mark-belbin/e-sup/mechanical/battery/HOLDER, PCBA, ASM.SLDASM

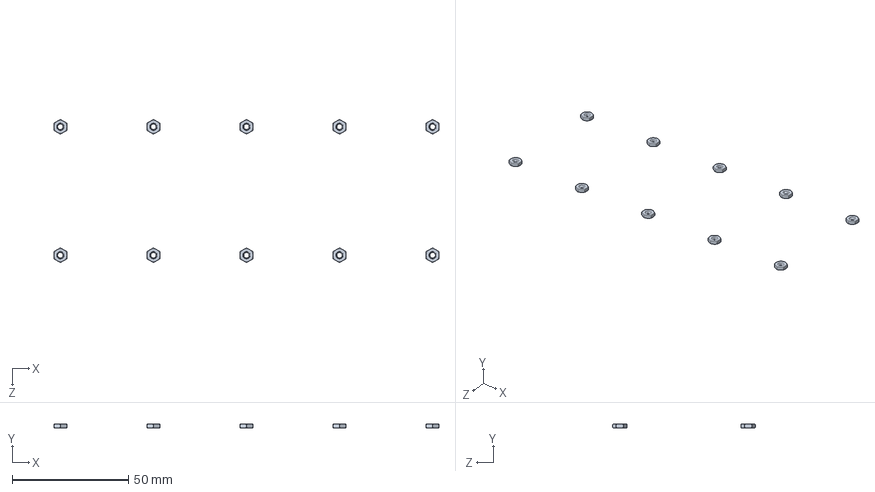
[picture p3: CAD file, 2023-11-13]
mechanical/battery/HOLDER, PCBA, ASM.SLDASM
165.5 x 1.80 x 61.6 mm
NUT, M3, THIN, 90370A203 x 10
