mark-belbin/e-sup/mechanical/battery/HOLDER, DUAL, ASM.SLDASM

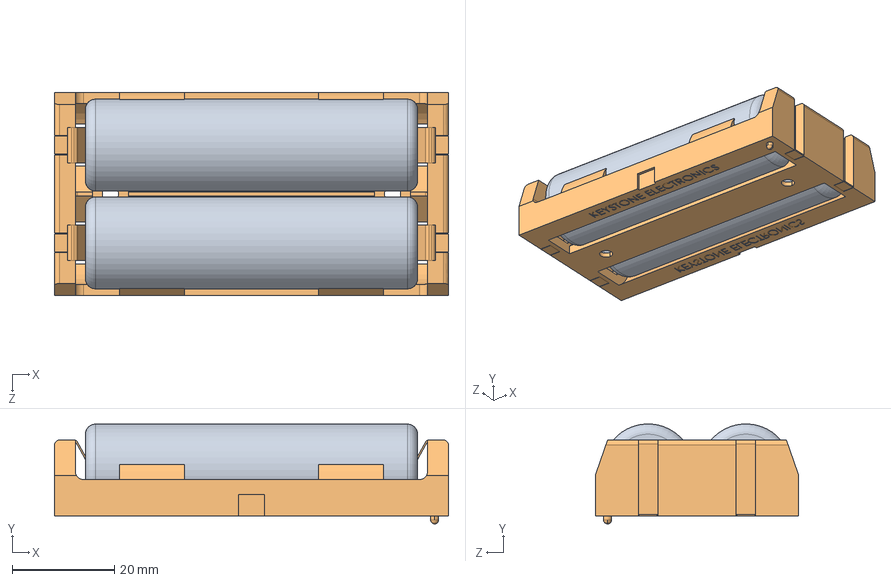
[picture p4: CAD file, 2023-11-13]
mechanical/battery/HOLDER, DUAL, ASM.SLDASM
77.1 x 19.5 x 39.8 mm
HOLDER, DUAL, KEYSTONE
BATTERY, 18650 x 2
