mark-belbin/e-sup/mechanical/battery/HOLDER, SINGLE, ASM.SLDASM

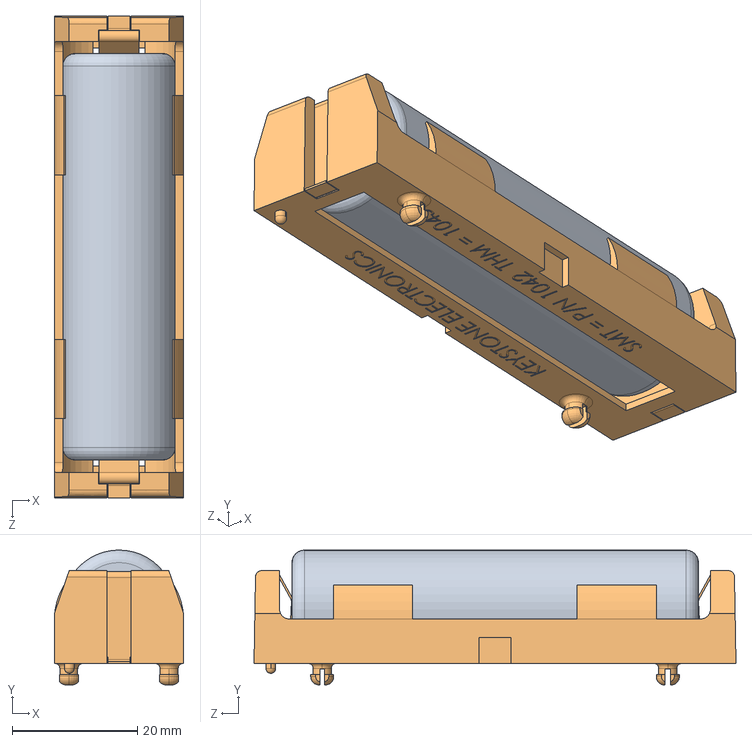
[picture p6: CAD file, 2023-10-09]
mechanical/battery/HOLDER, SINGLE, ASM.SLDASM
20.7 x 21.6 x 77.1 mm
HOLDER, SINGLE, KEYSTONE
BATTERY, 18650
