mark-belbin/e-sup/mechanical/ots_hardware/NUT, M3, THIN, 90370A203.SLDPRT

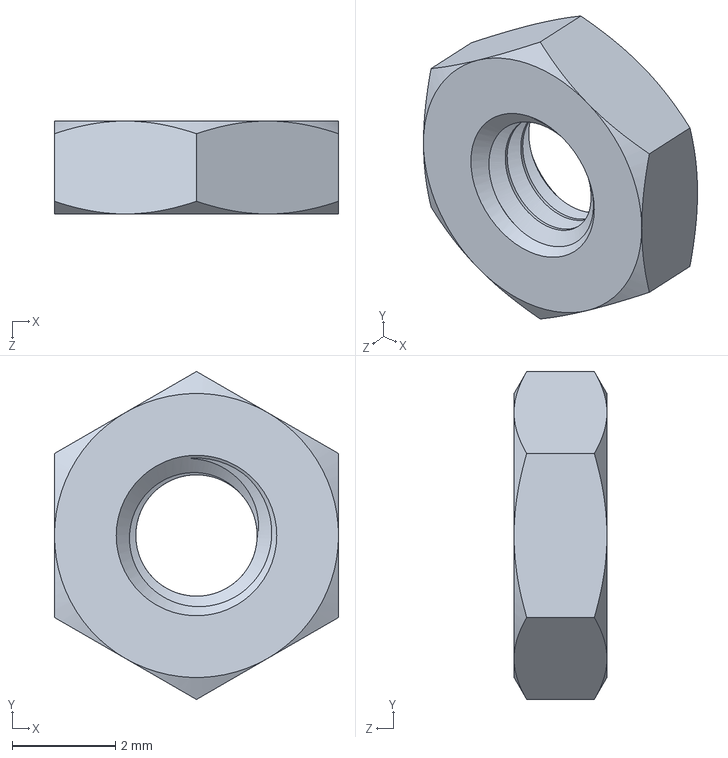
[picture p18: CAD file, 2023-10-09]
mechanical/ots_hardware/NUT, M3, THIN, 90370A203.SLDPRT
5.50 x 6.35 x 1.80 mm
