mark-belbin/e-sup/hardware/bms/3d_models/CUI_DEVICES_DS04-254-2-01BK-SMT-TR.step

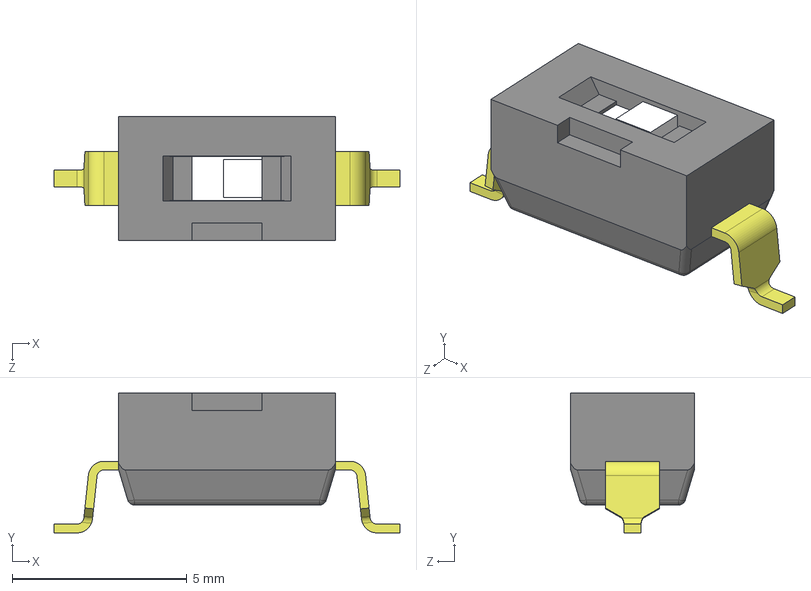
[picture p19: CAD file, 2024-04-14]
hardware/bms/3d_models/CUI_DEVICES_DS04-254-2-01BK-SMT-TR.step
9.90 x 4.00 x 3.54 mm
