mark-belbin/e-sup/mechanical/blue_robotics/WLP-M14-9.5MM-PUBLIC.SLDPRT

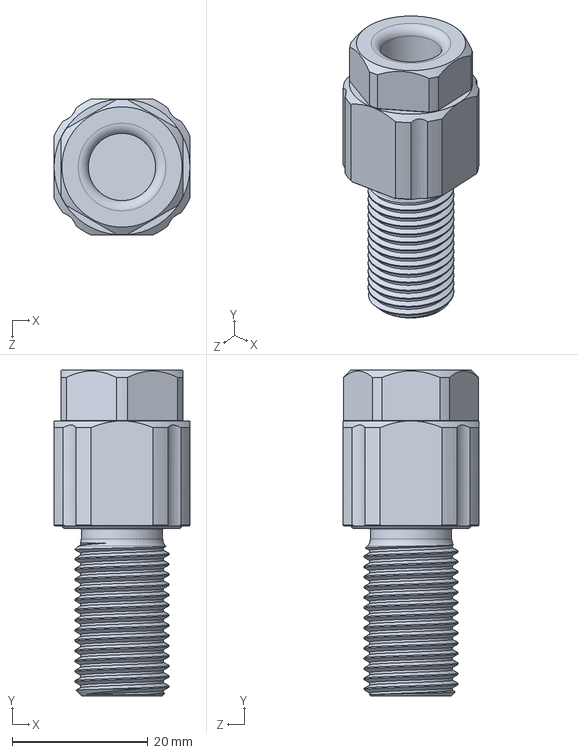
[picture p20: CAD file, 2023-10-09]
mechanical/blue_robotics/WLP-M14-9.5MM-PUBLIC.SLDPRT
20.0 x 48.0 x 20.0 mm
