mark-belbin/e-sup/mechanical/enclosure/ENCLOSURE, BODY.SLDPRT

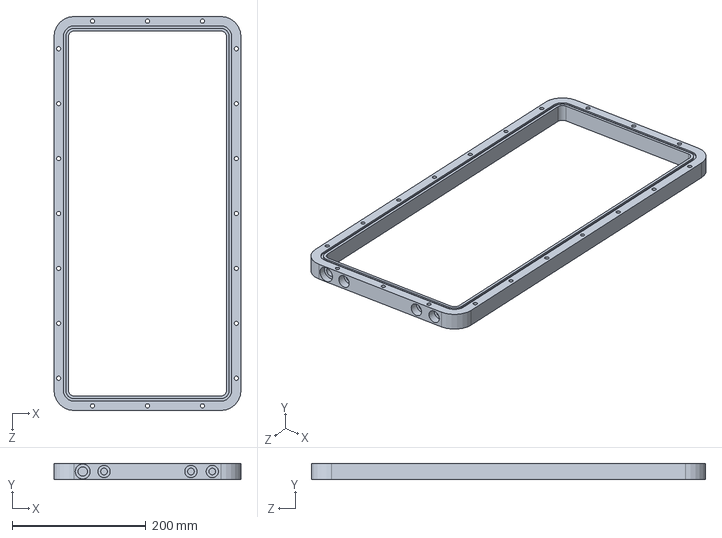
[picture p21: CAD file, 2023-10-09]
mechanical/enclosure/ENCLOSURE, BODY.SLDPRT
280.0 x 24.1 x 590.0 mm
