mark-belbin/e-sup/mechanical/battery/PCB, 11X BATTERY HOLDER.SLDPRT

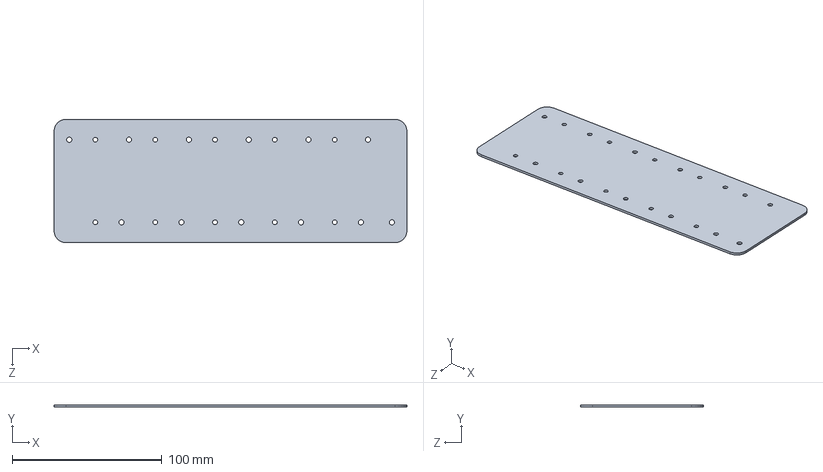
[picture p22: CAD file, 2023-10-31]
mechanical/battery/PCB, 11X BATTERY HOLDER.SLDPRT
236.0 x 1.60 x 82.5 mm
