mark-belbin/e-sup/mechanical/enclosure/ENCLOSURE, BASE.SLDPRT

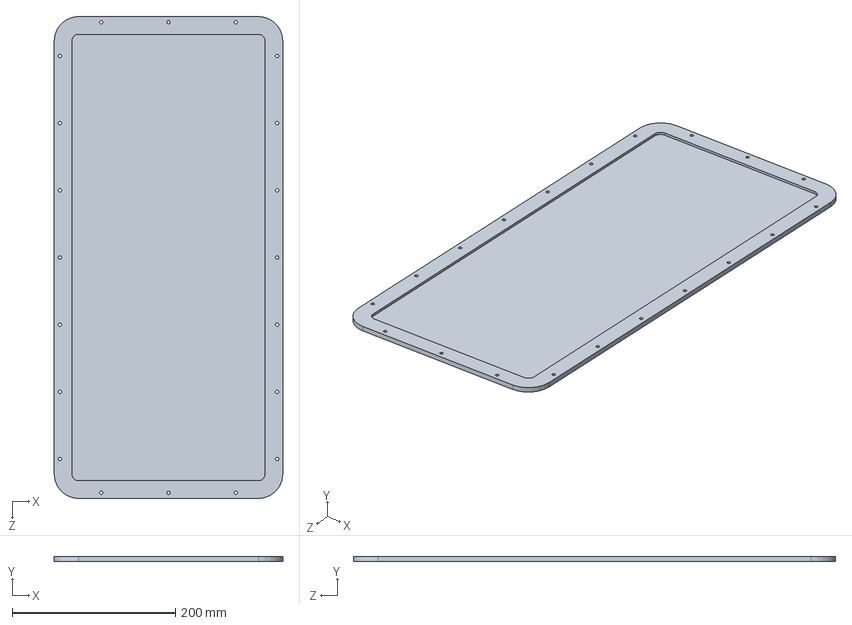
[picture p23: CAD file, 2023-10-09]
mechanical/enclosure/ENCLOSURE, BASE.SLDPRT
280.0 x 6.00 x 590.0 mm
