mark-belbin/e-sup/mechanical/battery/PCB, BMS.SLDPRT

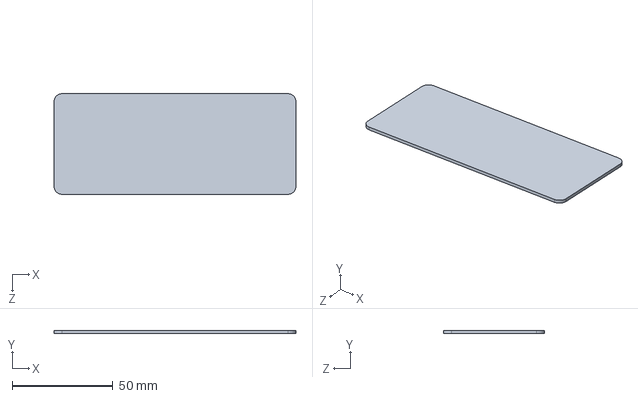
[picture p24: CAD file, 2023-10-31]
mechanical/battery/PCB, BMS.SLDPRT
120.0 x 1.60 x 50.0 mm
