mark-belbin/e-sup/mechanical/blue_robotics/SWITCH-M10-5A-R1-RP.SLDPRT

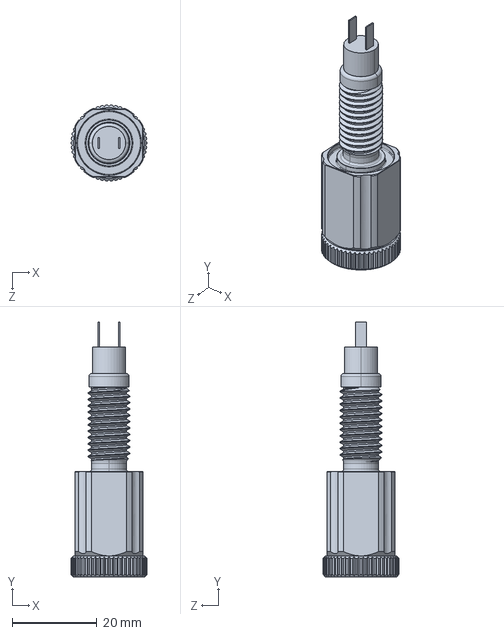
[picture p25: CAD file, 2023-10-09]
mechanical/blue_robotics/SWITCH-M10-5A-R1-RP.SLDPRT
18.0 x 60.3 x 18.0 mm
