mark-belbin/e-sup/mechanical/enclosure/ENCLOSURE, LID.SLDPRT

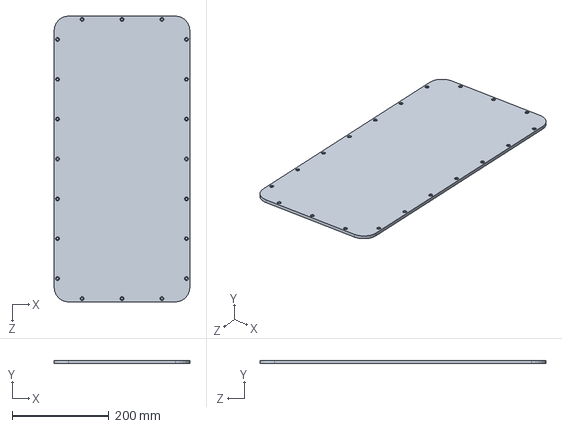
[picture p26: CAD file, 2023-10-09]
mechanical/enclosure/ENCLOSURE, LID.SLDPRT
280.0 x 6.35 x 590.0 mm
