mark-belbin/e-sup/mechanical/ots_hardware/INSERT, M4, 92398A123.SLDPRT

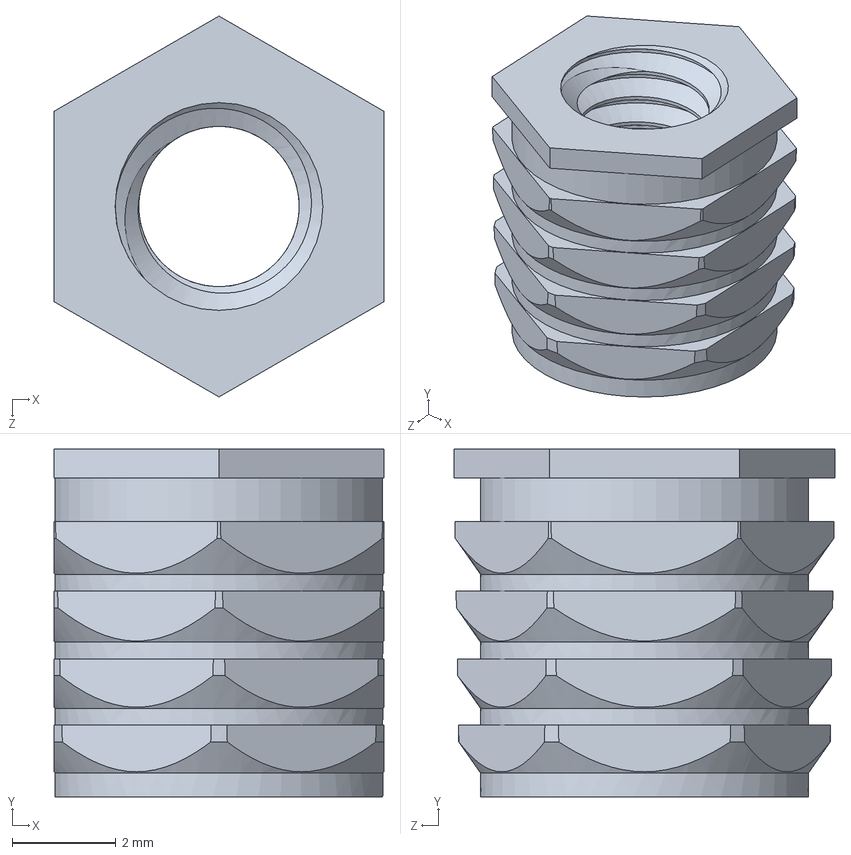
[picture p27: CAD file, 2023-10-09]
mechanical/ots_hardware/INSERT, M4, 92398A123.SLDPRT
6.35 x 6.70 x 7.33 mm
