mark-belbin/e-sup/hardware/bms/3d_models/SF-3812F-T.stp

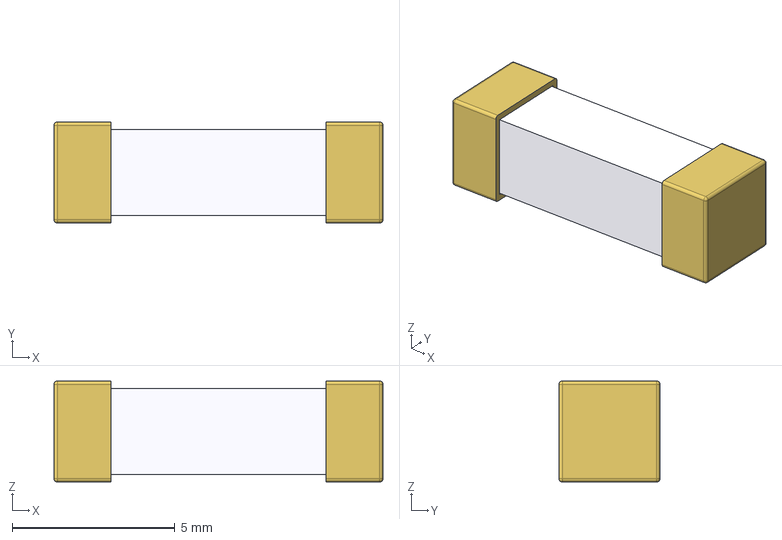
[picture p28: CAD file, 2024-04-14]
hardware/bms/3d_models/SF-3812F-T.stp
10.1 x 3.10 x 3.10 mm
