mark-belbin/e-sup/mechanical/battery/BATTERY, 18650.SLDPRT

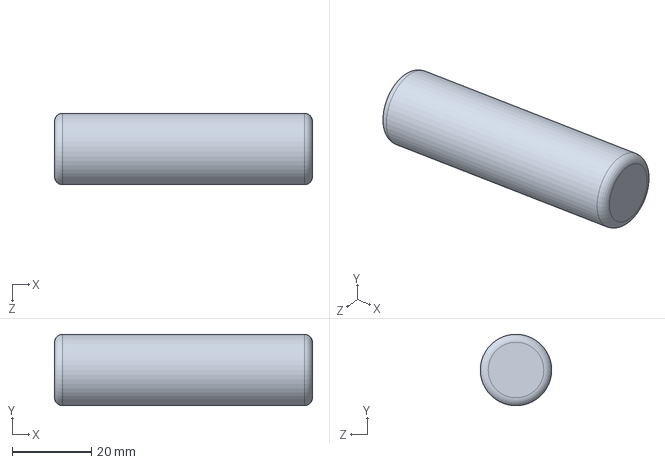
[picture p29: CAD file, 2023-10-09]
mechanical/battery/BATTERY, 18650.SLDPRT
65.0 x 18.0 x 18.0 mm
