mark-belbin/e-sup/mechanical/blue_robotics/WLP-M10-7.5MM-PUBLIC.SLDPRT

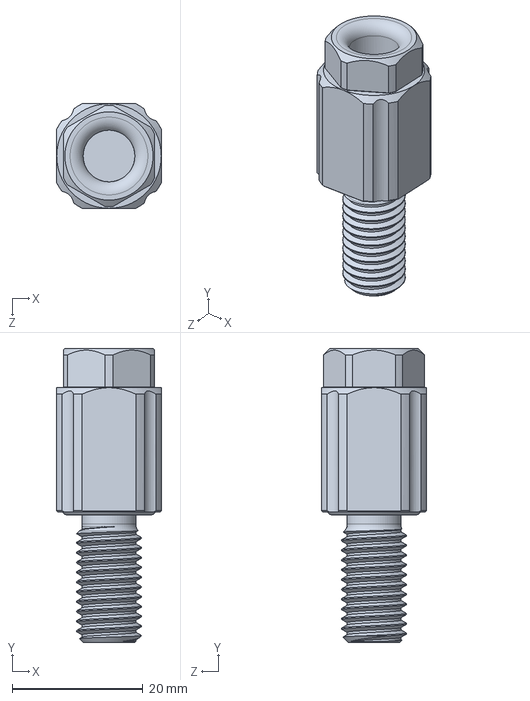
[picture p30: CAD file, 2023-10-09]
mechanical/blue_robotics/WLP-M10-7.5MM-PUBLIC.SLDPRT
16.0 x 45.0 x 16.0 mm
