mark-belbin/e-sup/hardware/bms/3d_models/IND_1050P-WE-PD_WRE.step

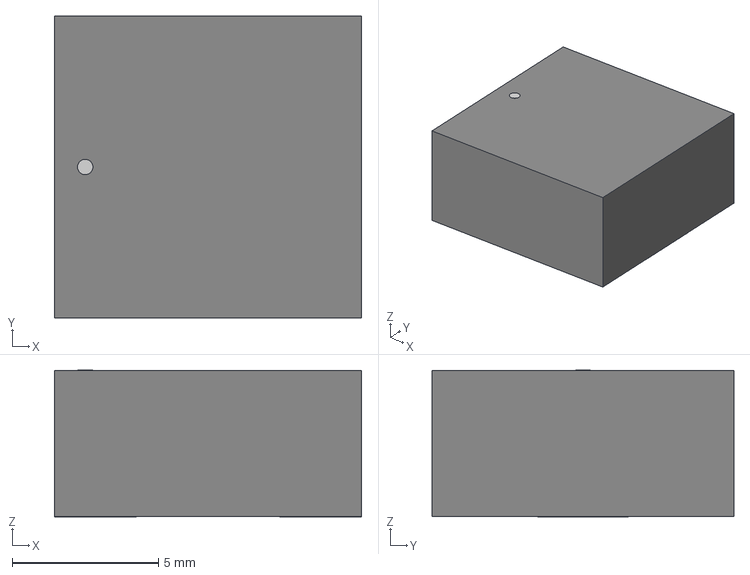
[picture p31: CAD file, 2024-04-14]
hardware/bms/3d_models/IND_1050P-WE-PD_WRE.step
10.5 x 10.3 x 5.01 mm
