mark-belbin/e-sup/mechanical/battery/HOLDER, SINGLE, KEYSTONE.SLDPRT

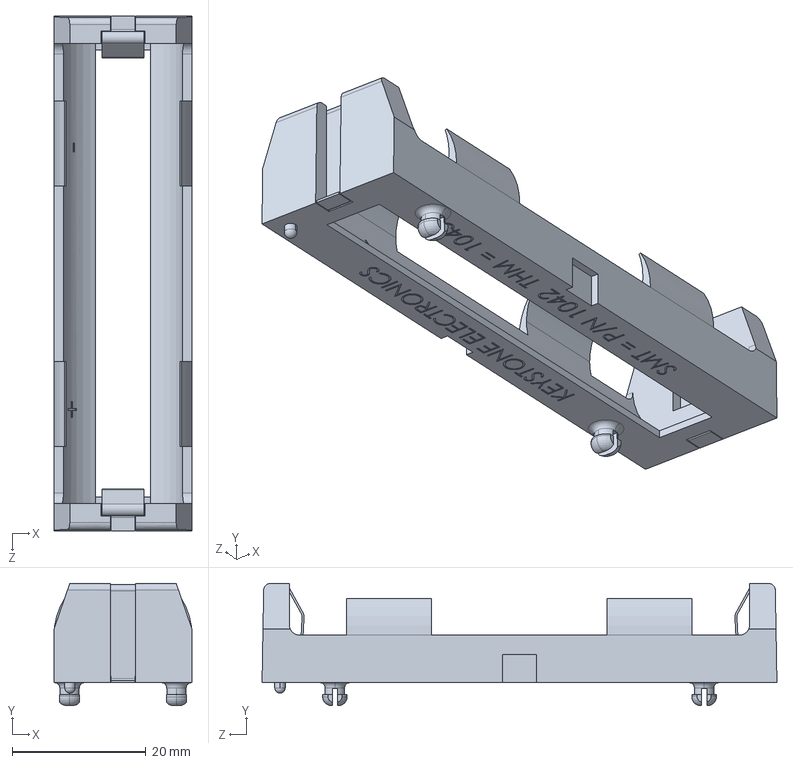
[picture p32: CAD file, 2023-10-09]
mechanical/battery/HOLDER, SINGLE, KEYSTONE.SLDPRT
20.7 x 18.3 x 77.1 mm
