mark-belbin/e-sup/mechanical/blue_robotics/VENT-M10-R1-RP.SLDPRT

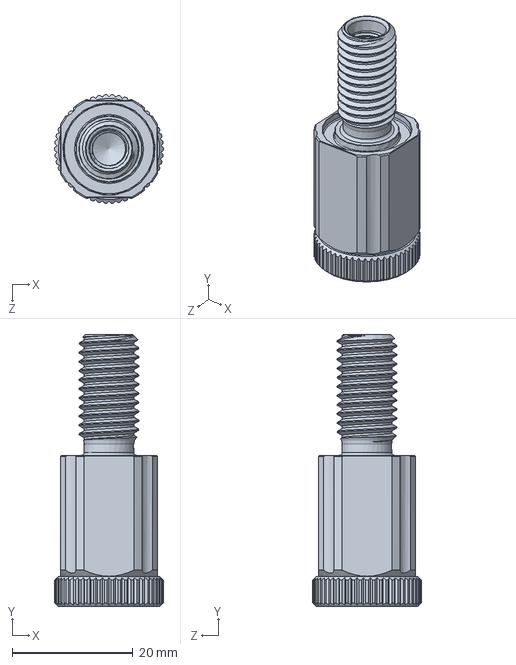
[picture p33: CAD file, 2023-10-09]
mechanical/blue_robotics/VENT-M10-R1-RP.SLDPRT
18.0 x 45.0 x 18.0 mm
