mark-belbin/e-sup/hardware/bms/3d_models/ETQP5M3R3YFK.step

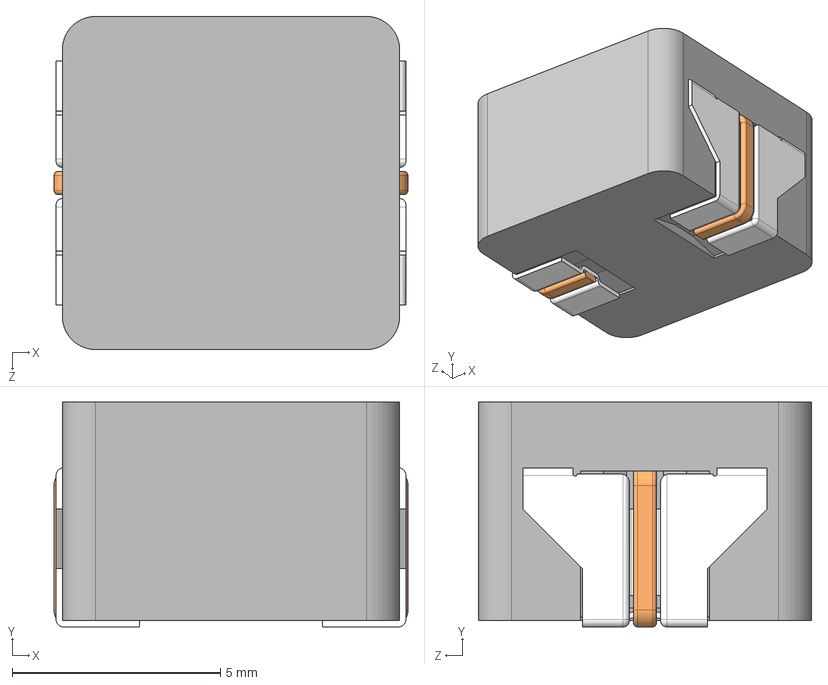
[picture p34: CAD file, 2024-04-14]
hardware/bms/3d_models/ETQP5M3R3YFK.step
8.50 x 5.40 x 8.00 mm
