mark-belbin/e-sup/hardware/bms/3d_models/5019.step

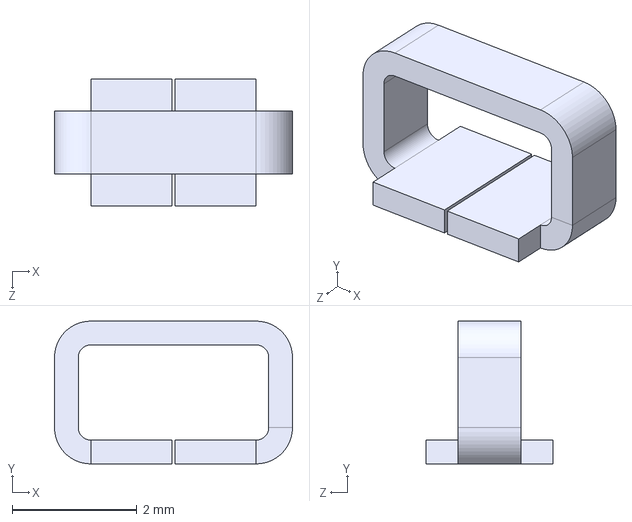
[picture p35: CAD file, 2024-04-14]
hardware/bms/3d_models/5019.step
3.81 x 2.29 x 2.03 mm
