mark-belbin/e-sup/hardware/bms/3d_models/usb4110-gf-a.stp

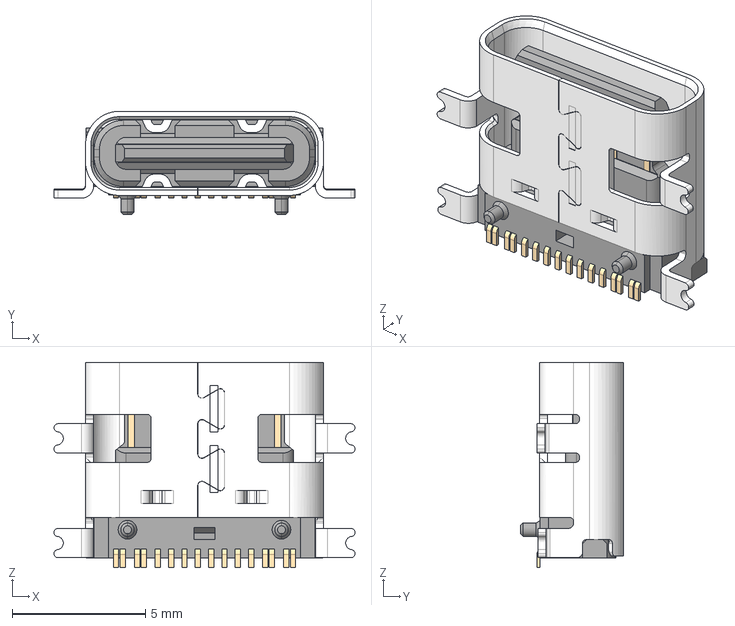
[picture p36: CAD file, 2024-04-14]
hardware/bms/3d_models/usb4110-gf-a.stp
11.3 x 3.89 x 7.70 mm
