mark-belbin/e-sup/hardware/bms/3d_models/B3U-1000P.step

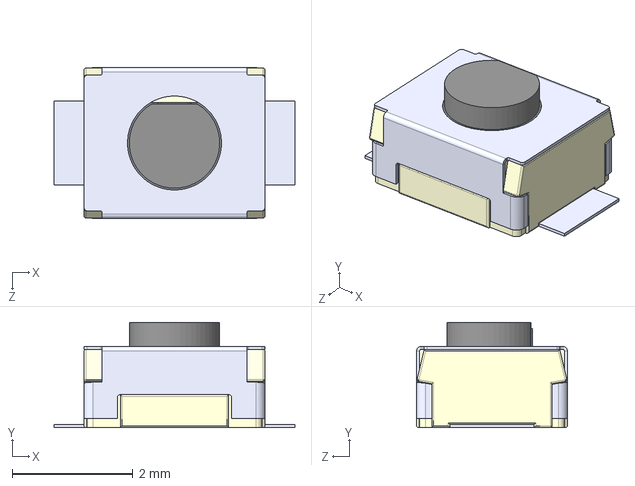
[picture p37: CAD file, 2024-04-14]
hardware/bms/3d_models/B3U-1000P.step
4.00 x 1.75 x 2.50 mm
