mark-belbin/e-sup/hardware/bms/3d_models/DCK0005A.stp

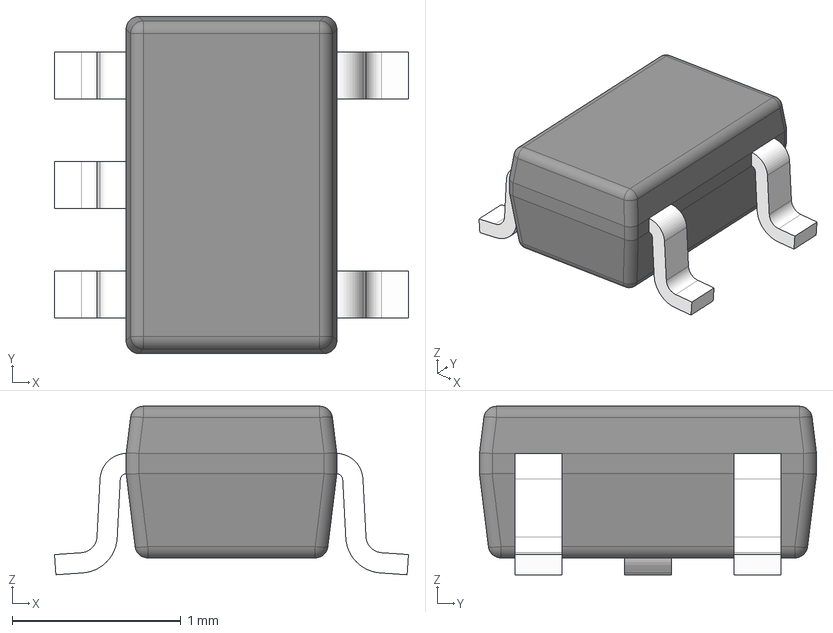
[picture p38: CAD file, 2024-04-14]
hardware/bms/3d_models/DCK0005A.stp
2.10 x 2.00 x 1.00 mm
BODY-SOT
LEAD-SOT x 5
PIN1-ID
