mark-belbin/e-sup/hardware/bms/3d_models/HCM1307-R.STEP

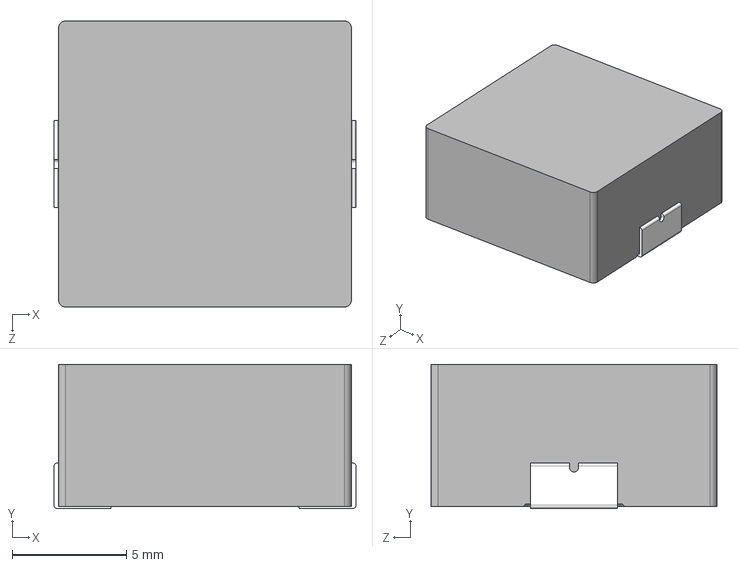
[picture p39: CAD file, 2024-04-14]
hardware/bms/3d_models/HCM1307-R.STEP
13.2 x 6.30 x 12.5 mm
