mark-belbin/e-sup/hardware/bms/3d_models/FUSE_0ACH-9800-TE_BEL.step

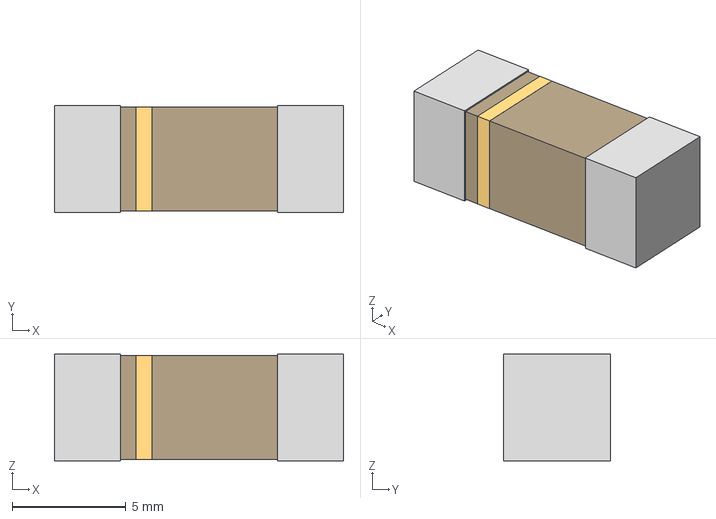
[picture p40: CAD file, 2024-04-14]
hardware/bms/3d_models/FUSE_0ACH-9800-TE_BEL.step
12.7 x 4.70 x 4.70 mm
